cavesLezet/Eth_switch_1gbit/photo_2018-03-01_10-21-31.jpg

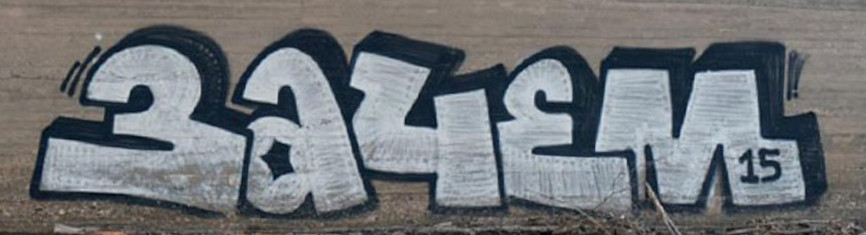
photo_2018-03-01_10-21-31.jpg
