cavesLezet/Eth_switch_1gbit/photo_2018_03_01_10_21_31_edge.png

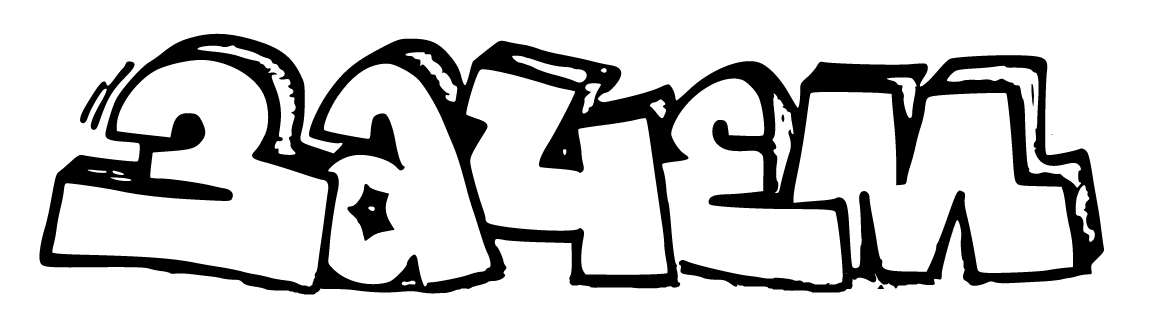
photo_2018_03_01_10_21_31_edge.png
